DimChik2903/ardubasto/docs/images/Colored_schema_telestart.jpg

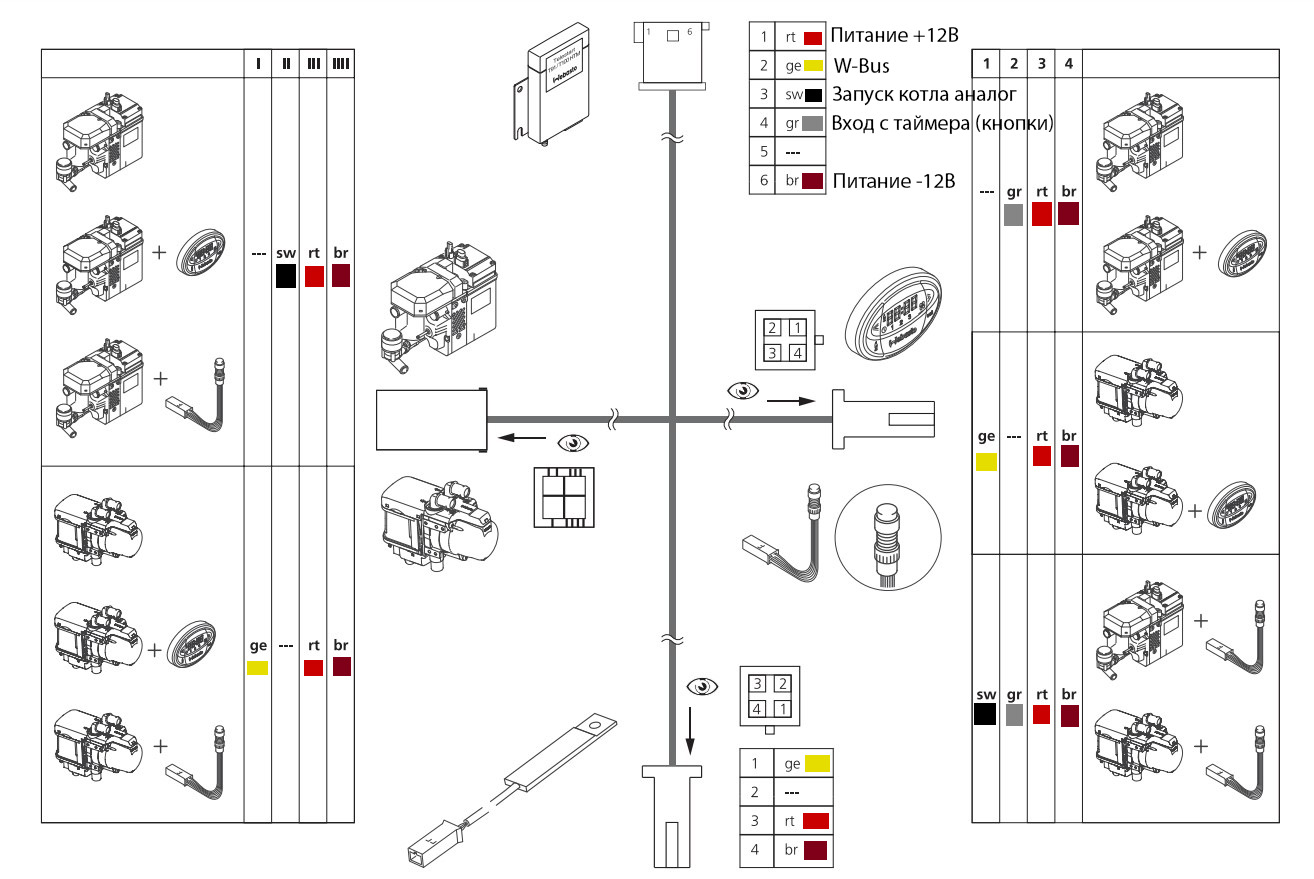
docs/images/Colored_schema_telestart.jpg
