DimChik2903/ardubasto/docs/images/First_schema.jpg

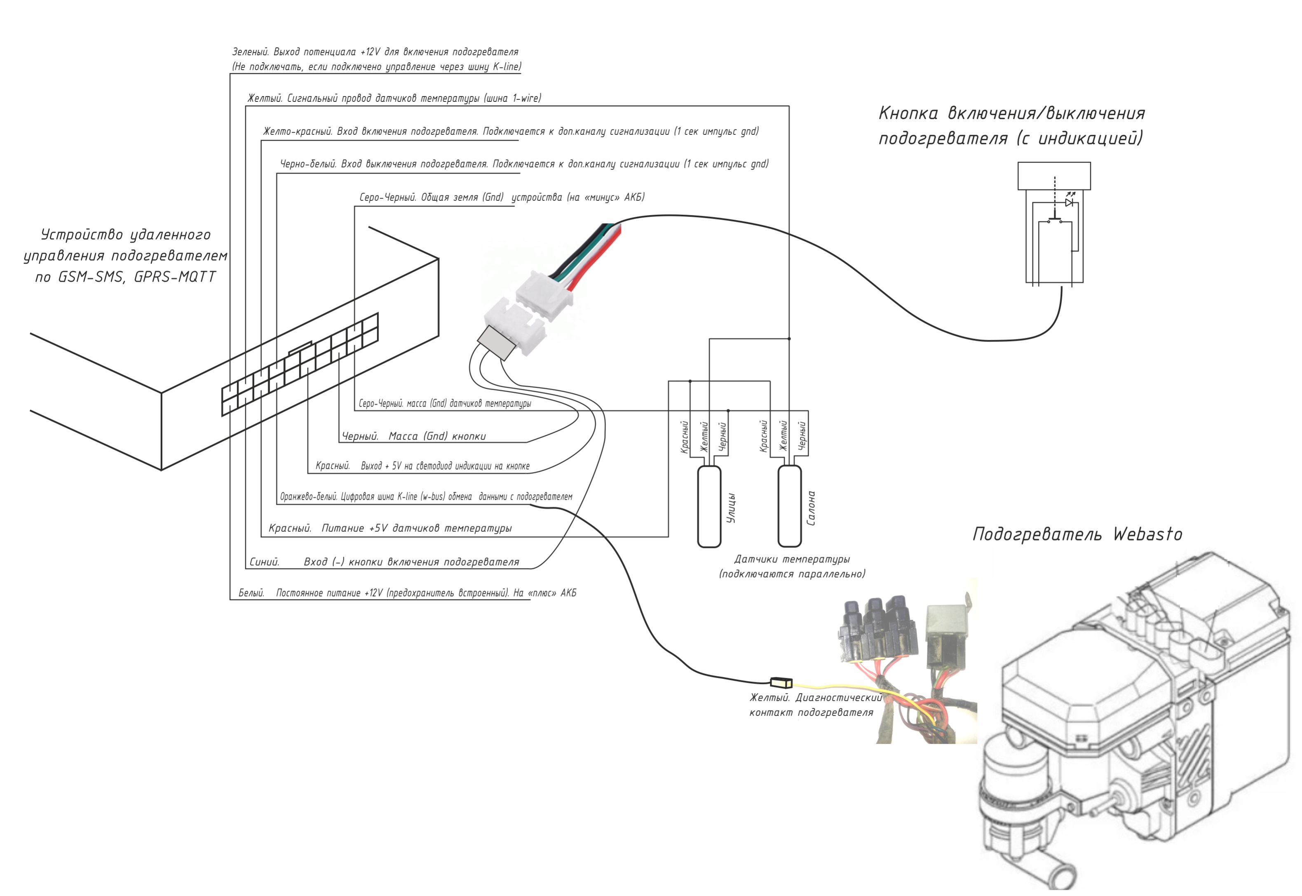
docs/images/First_schema.jpg
