DimChik2903/ardubasto/docs/images/My_device.jpg

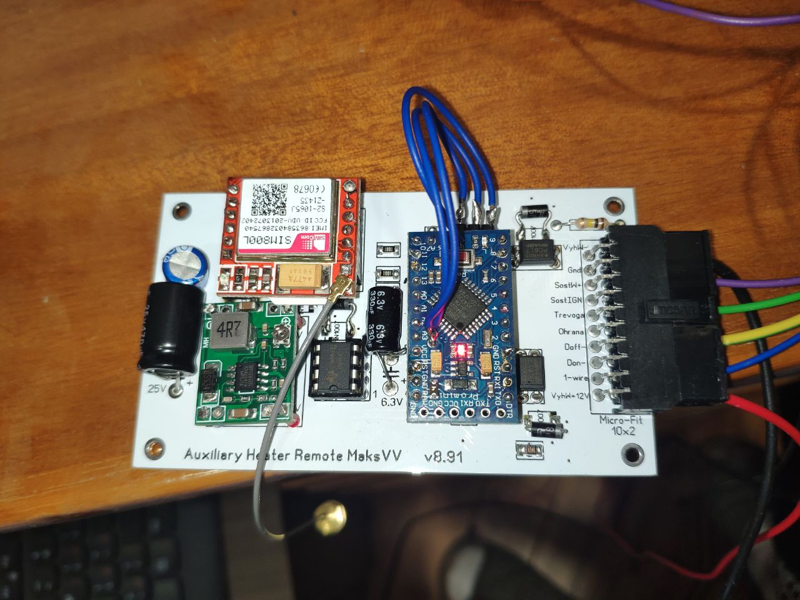
docs/images/My_device.jpg
