DimChik2903/ardubasto/docs/images/WriteNumber1.png

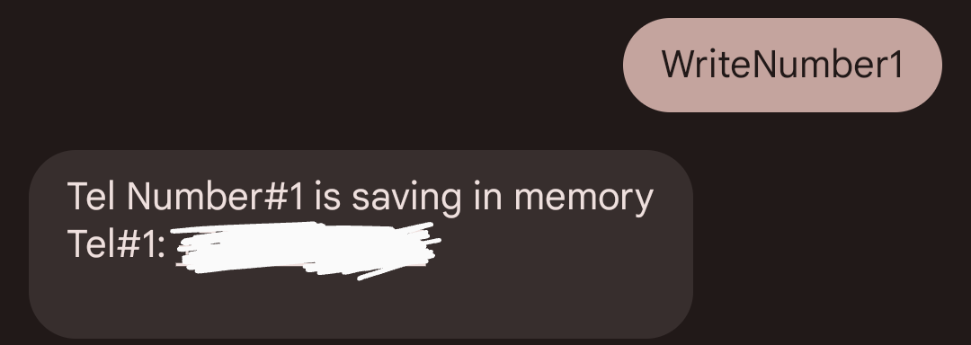
docs/images/WriteNumber1.png
