DimChik2903/ardubasto/docs/MQTT Dash/10.jpg

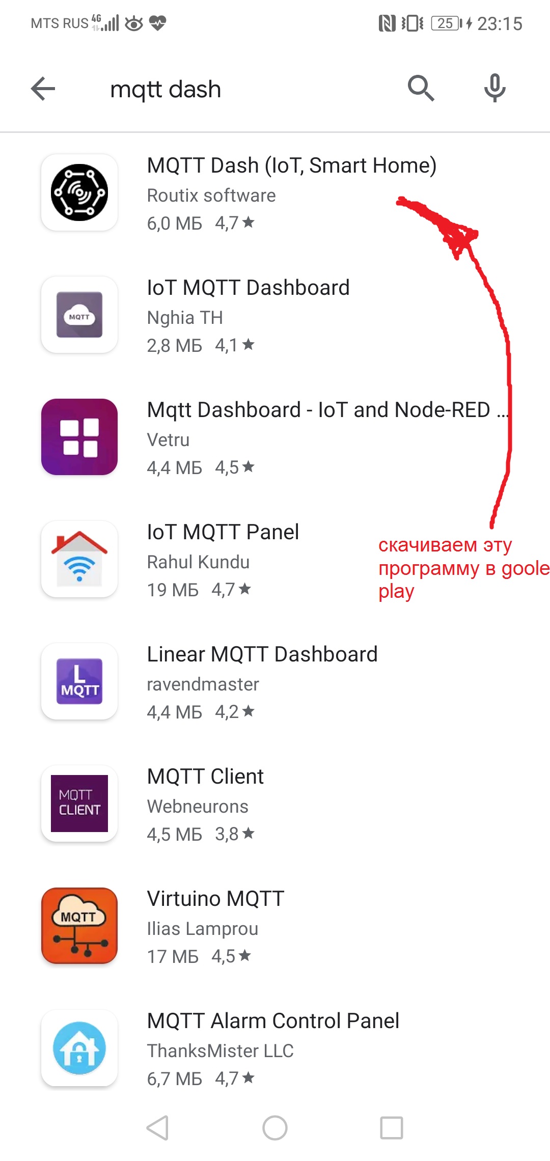
docs/MQTT Dash/10.jpg
