DimChik2903/ardubasto/docs/MQTT Dash/11.jpg

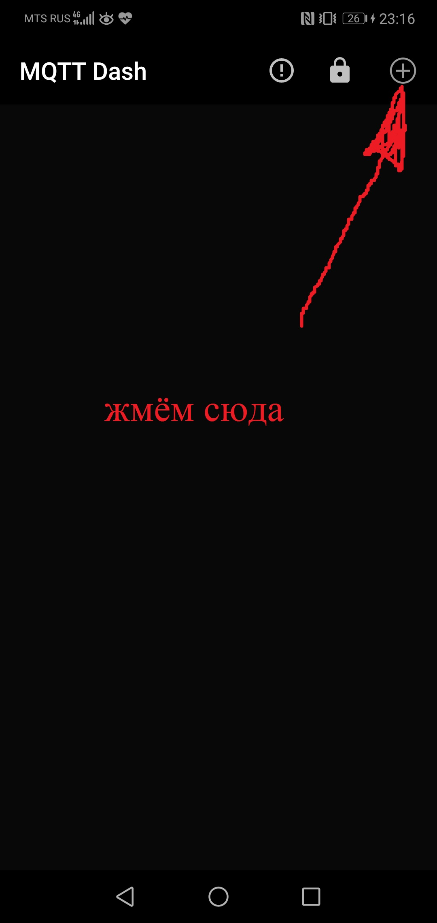
docs/MQTT Dash/11.jpg
