DimChik2903/ardubasto/docs/MQTT Dash/12.jpg

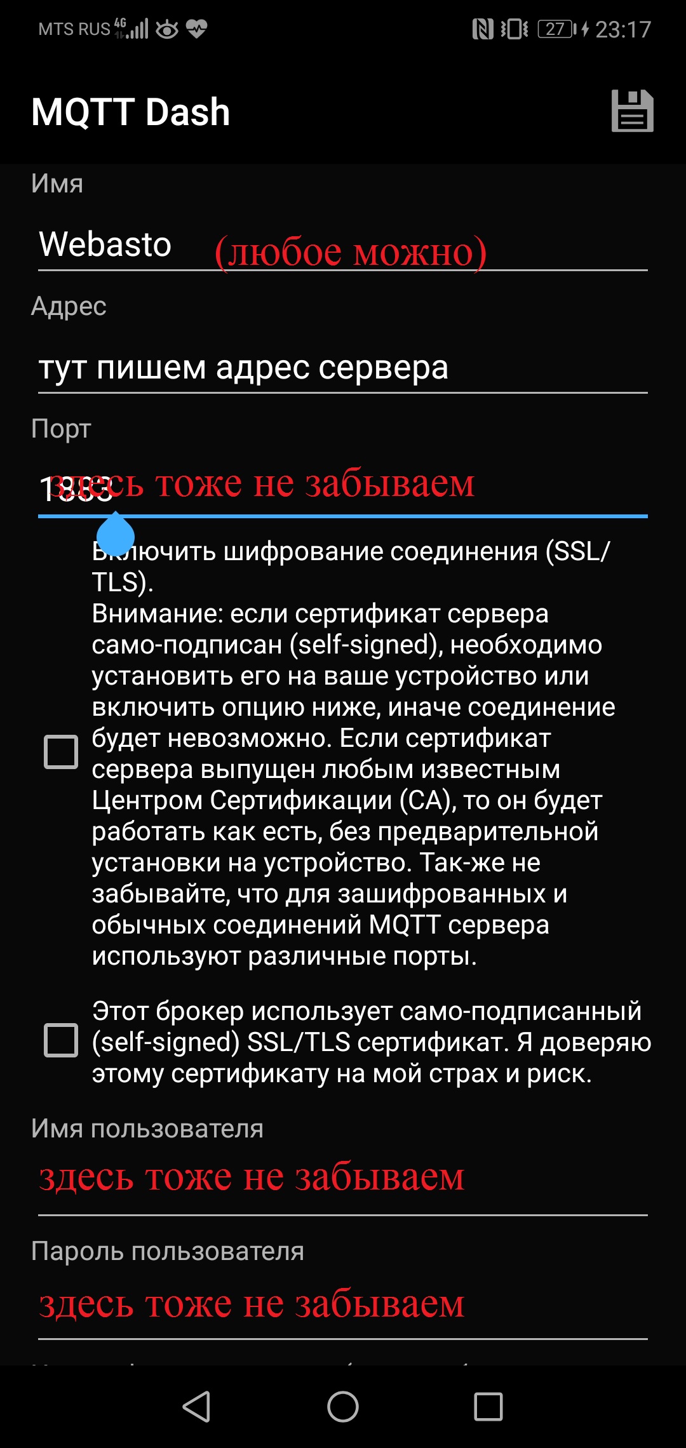
docs/MQTT Dash/12.jpg
