DimChik2903/ardubasto/docs/MQTT Dash/13.jpg

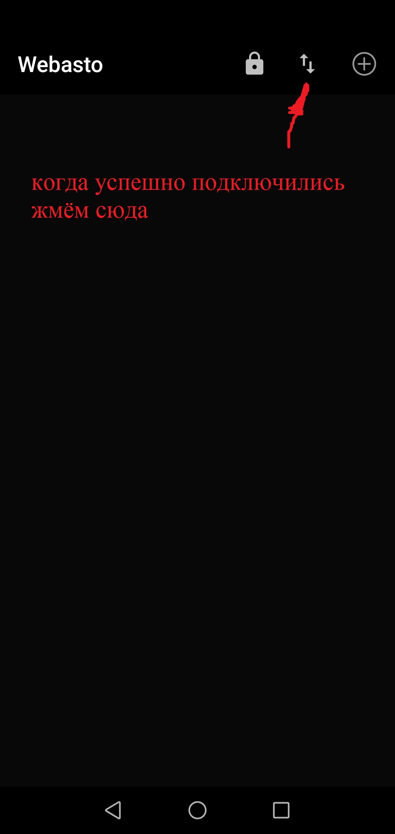
docs/MQTT Dash/13.jpg
