DimChik2903/ardubasto/docs/MQTT Dash/14.jpg

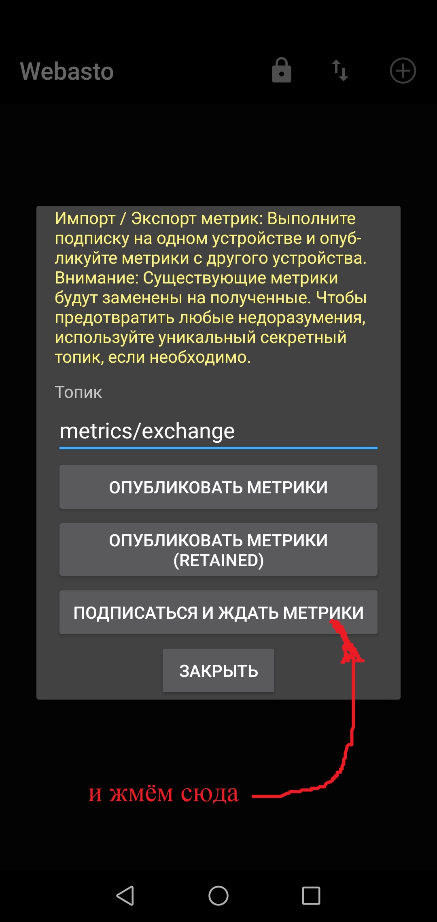
docs/MQTT Dash/14.jpg
