DimChik2903/ardubasto/docs/MQTT Dash/15.jpg

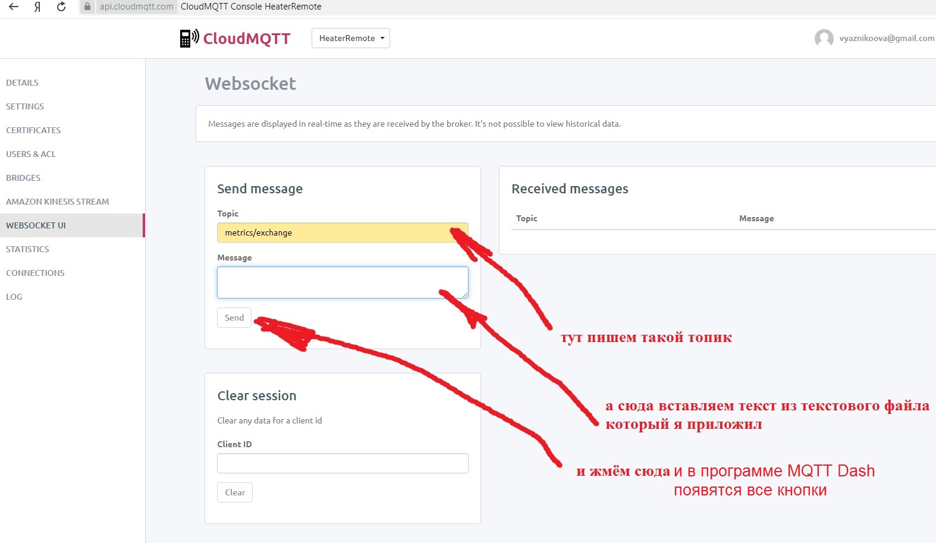
docs/MQTT Dash/15.jpg
