DimChik2903/ardubasto/docs/MQTT Dash/16.jpg

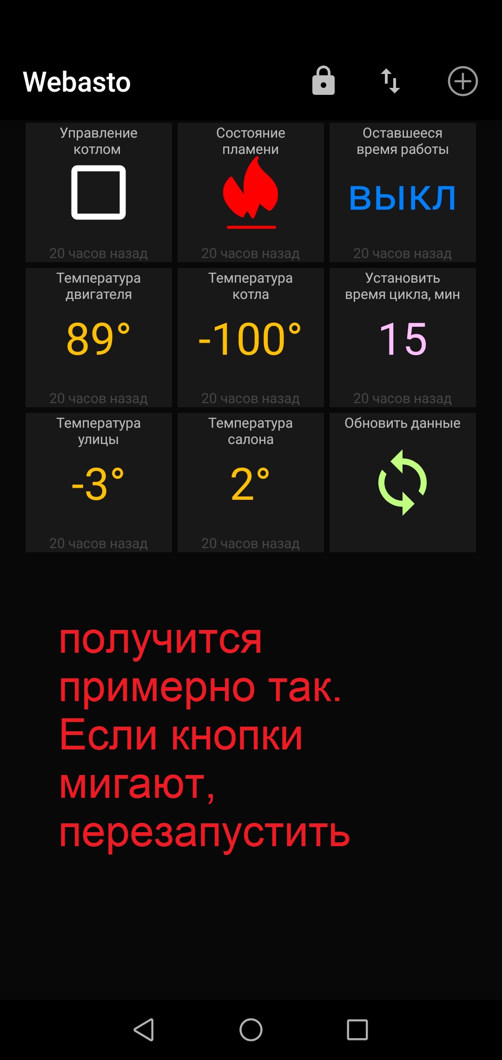
docs/MQTT Dash/16.jpg
