DimChik2903/ardubasto/docs/Запуск MQTT/1.jpg

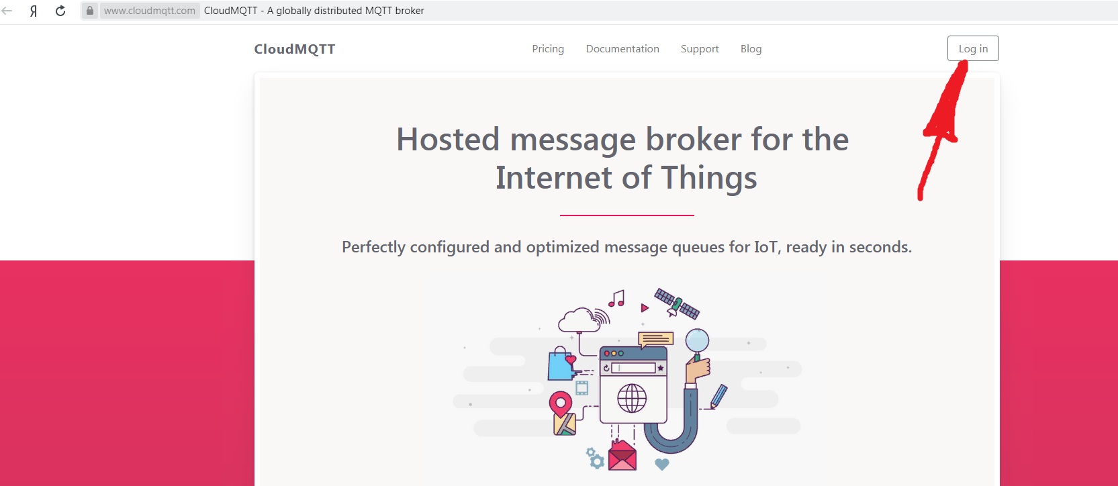
docs/Запуск MQTT/1.jpg
