DimChik2903/ardubasto/docs/Запуск MQTT/2.jpg

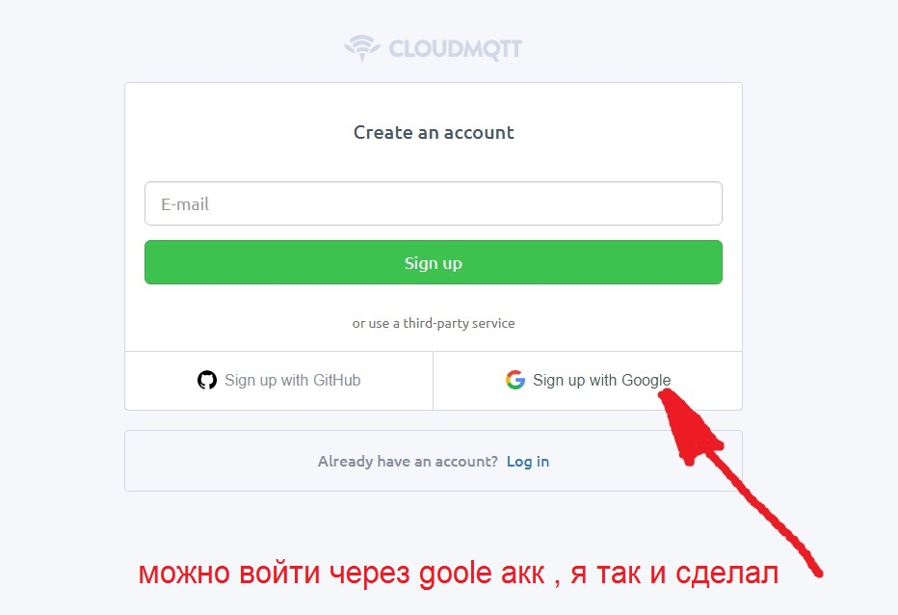
docs/Запуск MQTT/2.jpg
