DimChik2903/ardubasto/docs/Запуск MQTT/3.jpg

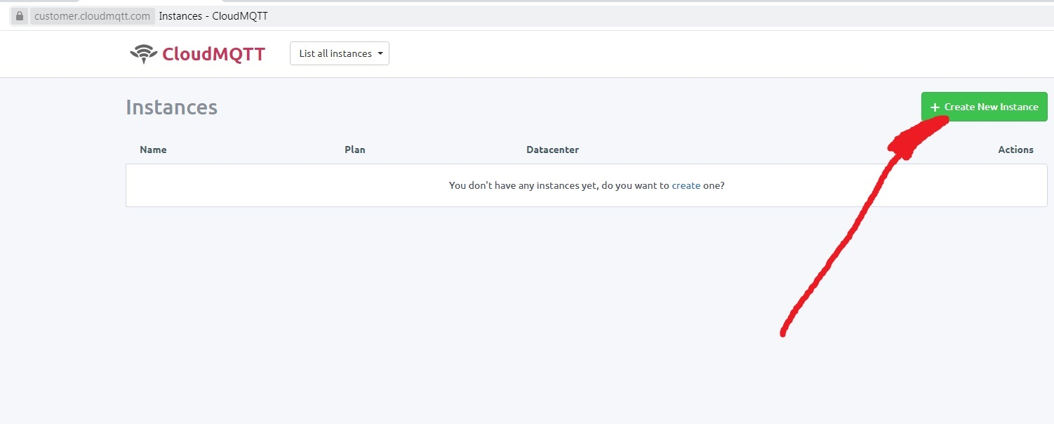
docs/Запуск MQTT/3.jpg
