DimChik2903/ardubasto/docs/Запуск MQTT/4.jpg

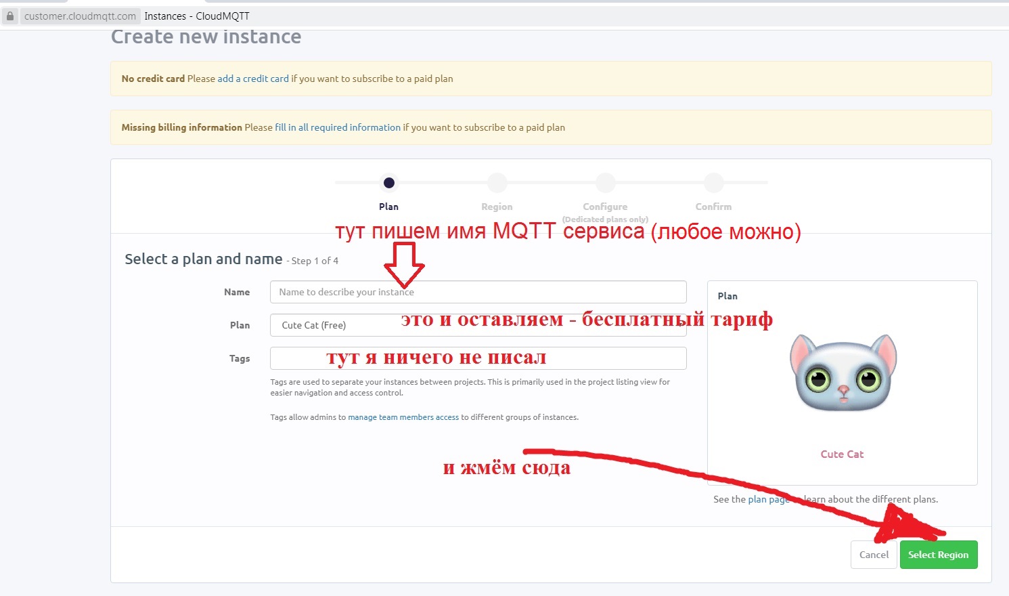
docs/Запуск MQTT/4.jpg
