DimChik2903/ardubasto/docs/Запуск MQTT/5.jpg

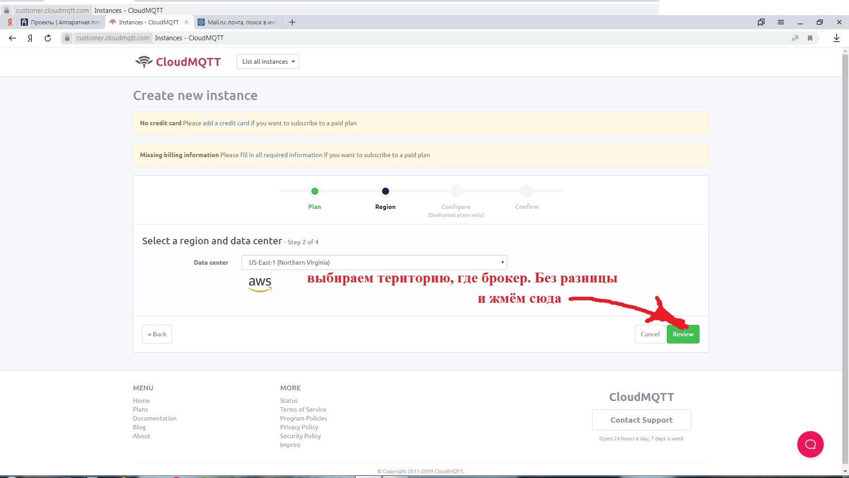
docs/Запуск MQTT/5.jpg
