DimChik2903/ardubasto/docs/Запуск MQTT/6.jpg

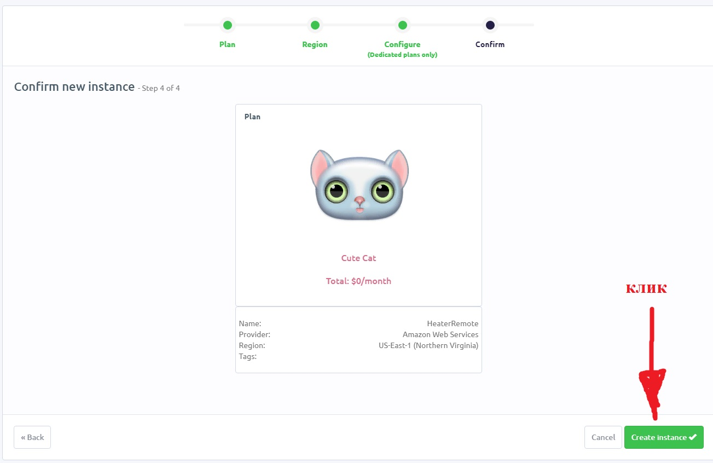
docs/Запуск MQTT/6.jpg
