DimChik2903/ardubasto/docs/Запуск MQTT/7.jpg

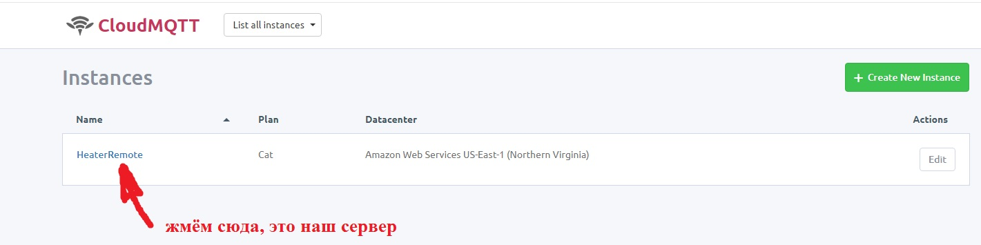
docs/Запуск MQTT/7.jpg
