DimChik2903/ardubasto/docs/Запуск MQTT/8.jpg

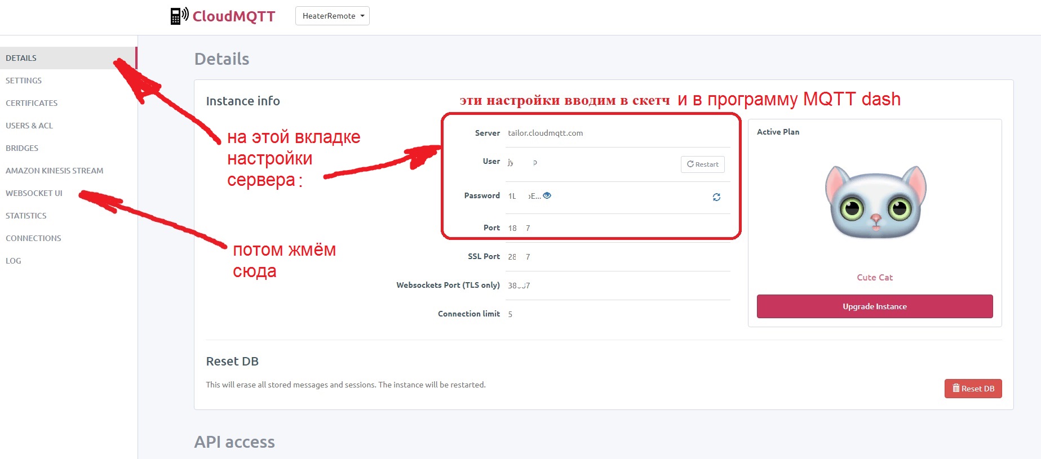
docs/Запуск MQTT/8.jpg
