DimChik2903/ardubasto/docs/Запуск MQTT/9.jpg

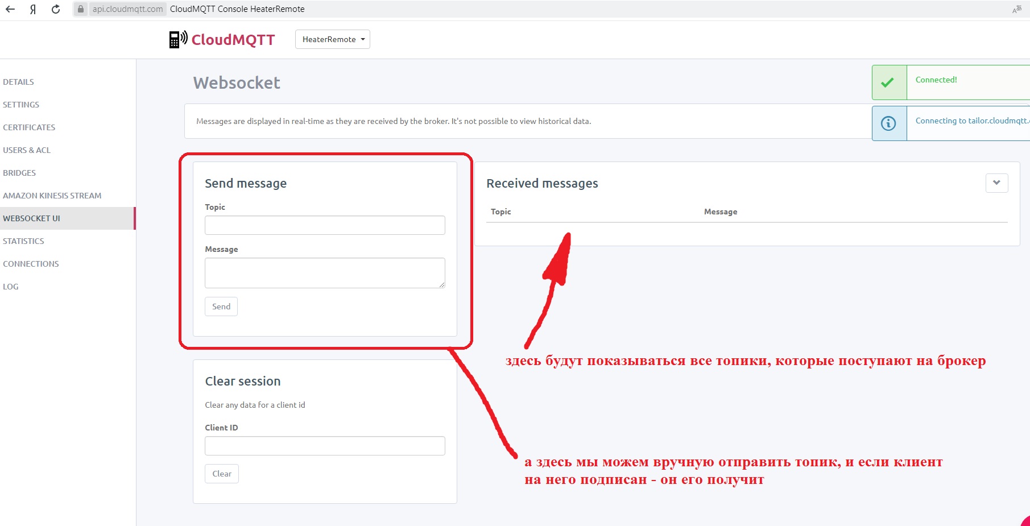
docs/Запуск MQTT/9.jpg
